PLUGSi/PLUGSi/PCB/1. Plug Base/Plug Base Circuit.png

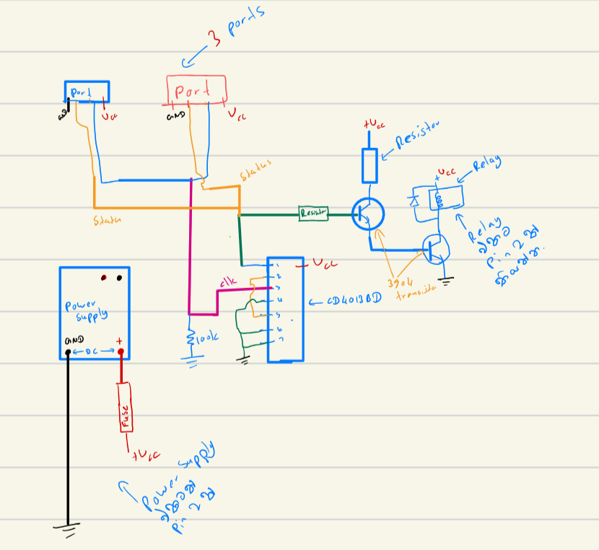
PCB/1. Plug Base/Plug Base Circuit.png
