PLUGSi/PLUGSi/PCB/2. Reprogrammable Timer/Timer Circuit.png

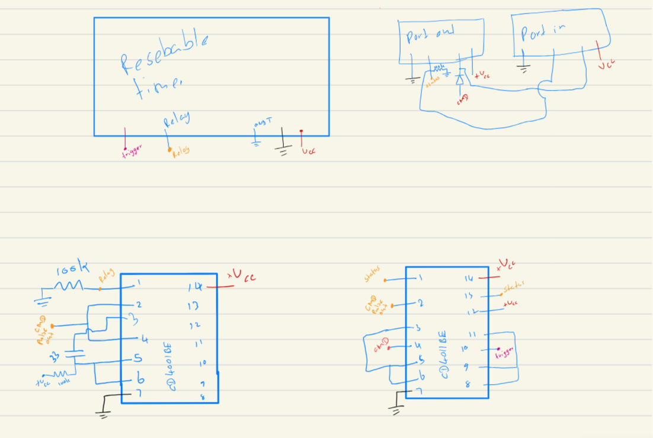
PCB/2. Reprogrammable Timer/Timer Circuit.png
