PLUGSi/PLUGSi/PCB/3. Set Timer/Set Timer Circuit.png

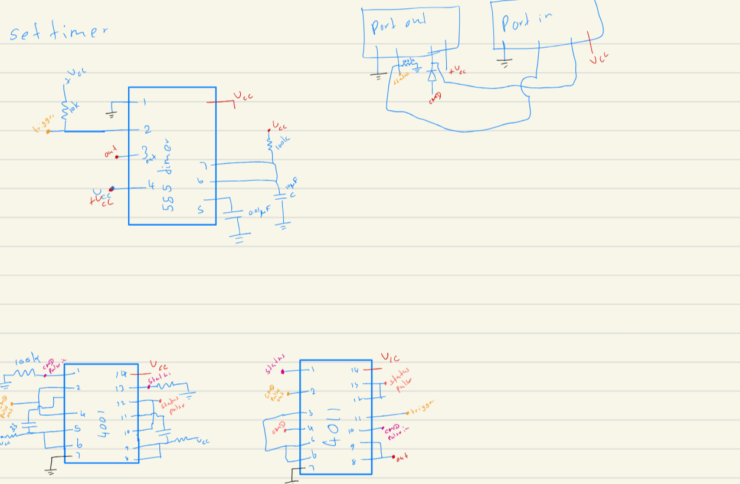
PCB/3. Set Timer/Set Timer Circuit.png
