PLUGSi/PLUGSi/Enclosure/Base/Base_Back.SLDPRT

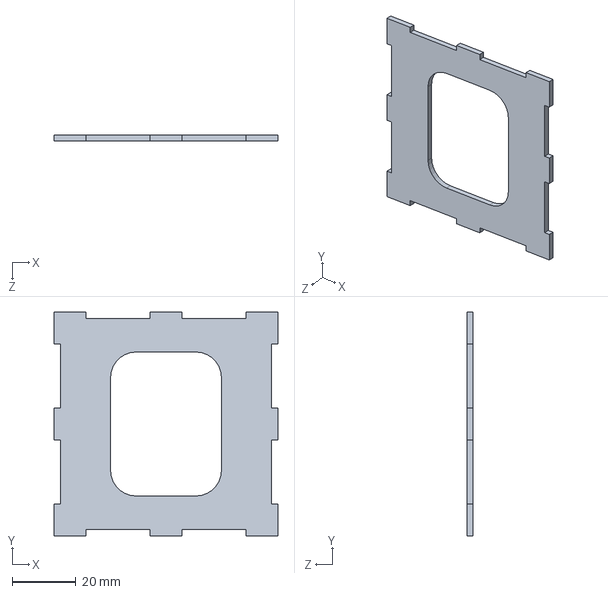
[picture p69: CAD file, 2024-06-27]
Enclosure/Base/Base_Back.SLDPRT
70.0 x 70.0 x 2.00 mm
