PLUGSi/PLUGSi/Enclosure/Module_Normal/DXF/Black/Module_LR_Female-1.DXF

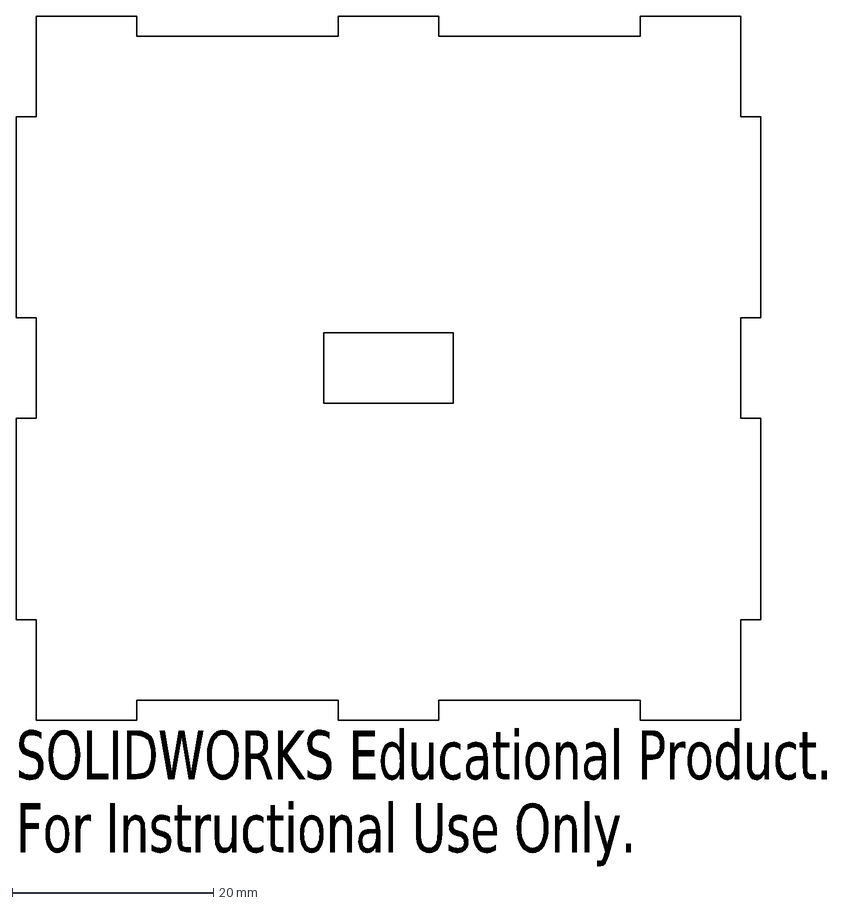
[picture p70: CAD file, 2024-06-27]
Enclosure/Module_Normal/DXF/Black/Module_LR_Female-1.DXF
SOLIDWORKS Educational Product.
For Instructional Use Only.
