PLUGSi/PLUGSi/Enclosure/Base/220ACto5VDC.SLDPRT

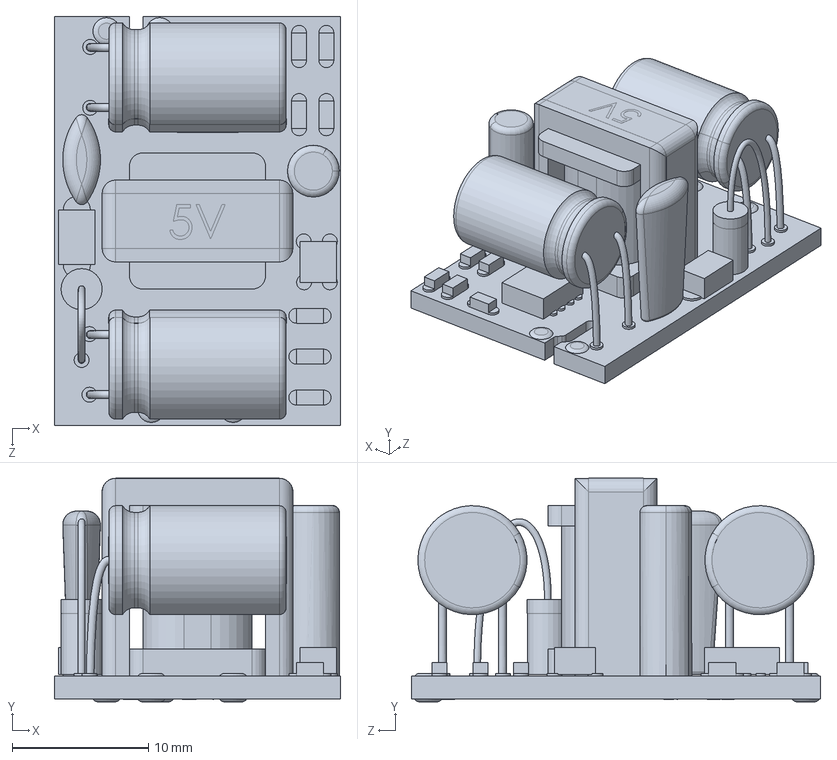
[picture p71: CAD file, 2024-06-27]
Enclosure/Base/220ACto5VDC.SLDPRT
21.0 x 16.4 x 30.0 mm
