PLUGSi/PLUGSi/Enclosure/Module/Module_Back.SLDPRT

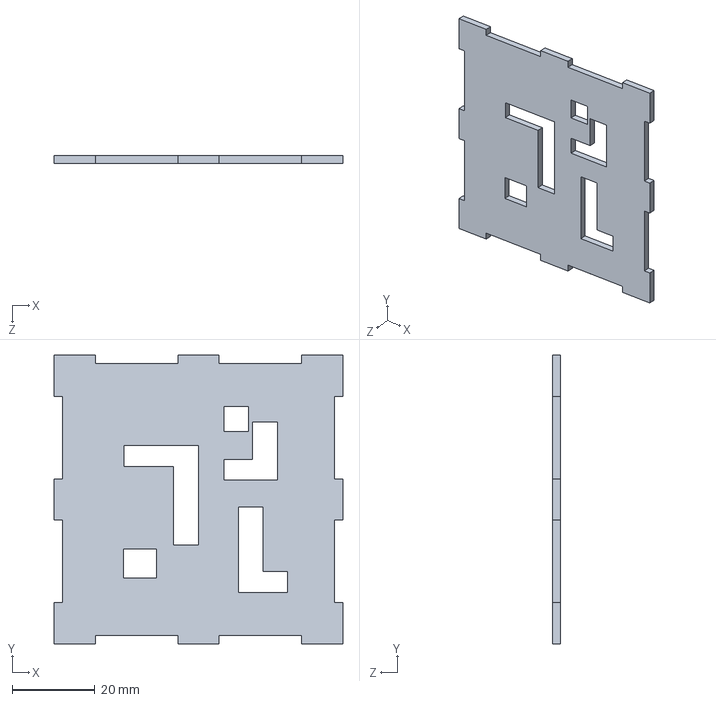
[picture p72: CAD file, 2024-06-27]
Enclosure/Module/Module_Back.SLDPRT
70.0 x 70.0 x 2.00 mm
