PLUGSi/PLUGSi/Enclosure/Module_Normal/Black_Cover.SLDPRT

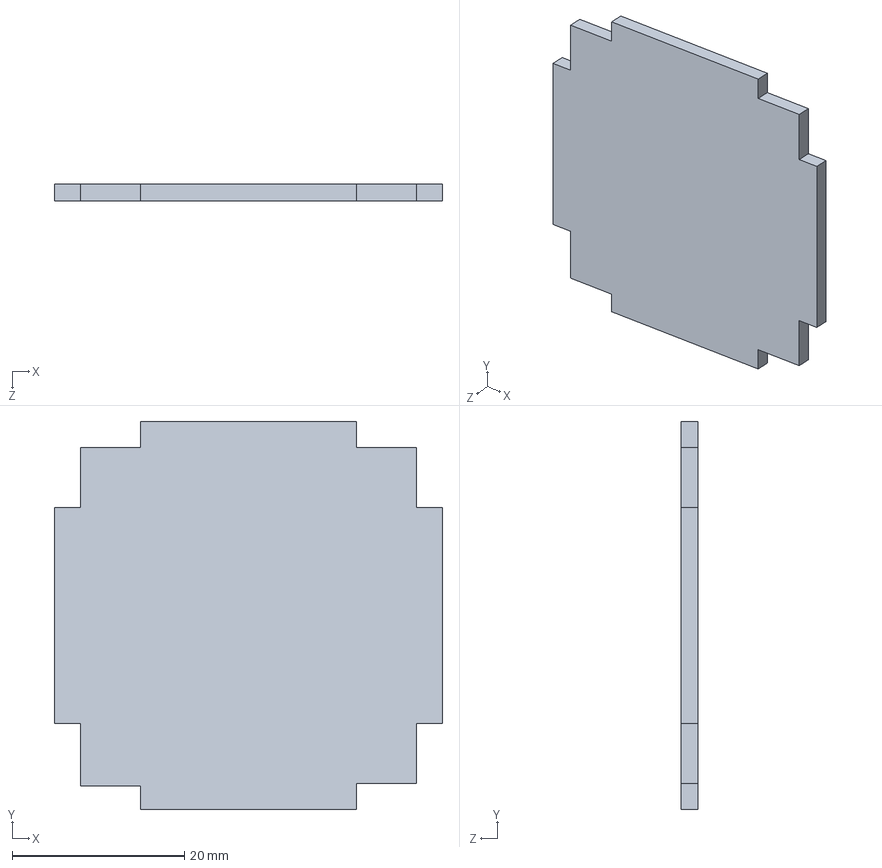
[picture p73: CAD file, 2024-06-27]
Enclosure/Module_Normal/Black_Cover.SLDPRT
45.0 x 45.0 x 2.00 mm
