PLUGSi/PLUGSi/Enclosure/Module/port_1.SLDPRT

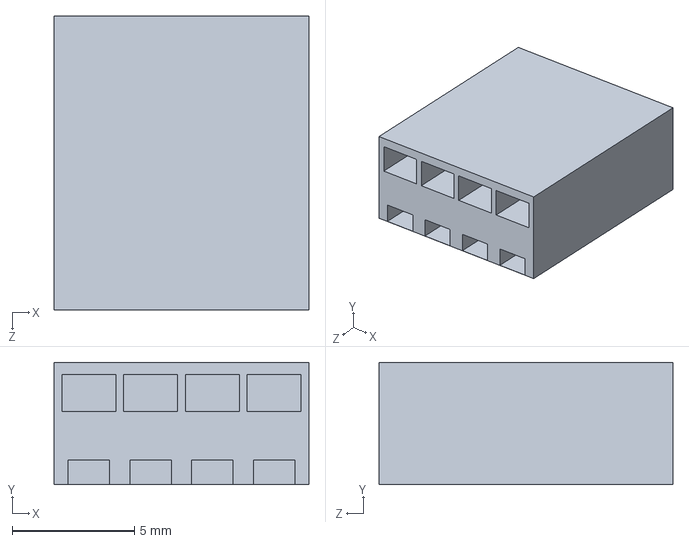
[picture p74: CAD file, 2024-06-27]
Enclosure/Module/port_1.SLDPRT
10.4 x 5.00 x 12.0 mm
