PLUGSi/PLUGSi/Enclosure/Base/Base_Plug_Front.SLDPRT

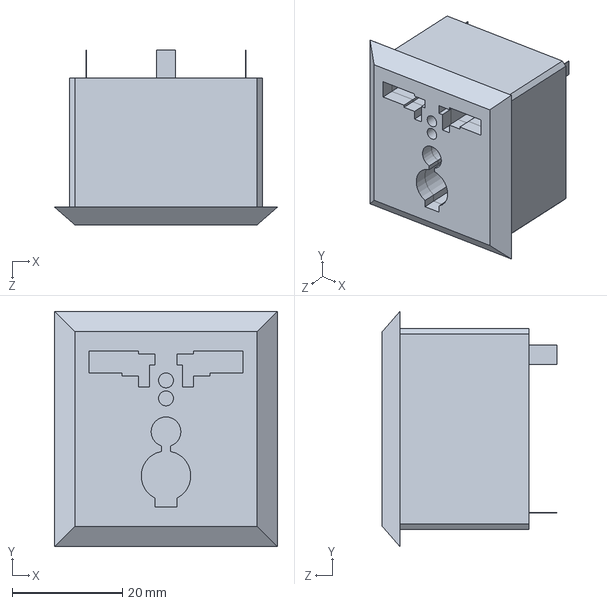
[picture p75: CAD file, 2024-06-27]
Enclosure/Base/Base_Plug_Front.SLDPRT
40.5 x 42.7 x 31.7 mm
