PLUGSi/PLUGSi/Enclosure/Module/Module_Front.SLDPRT

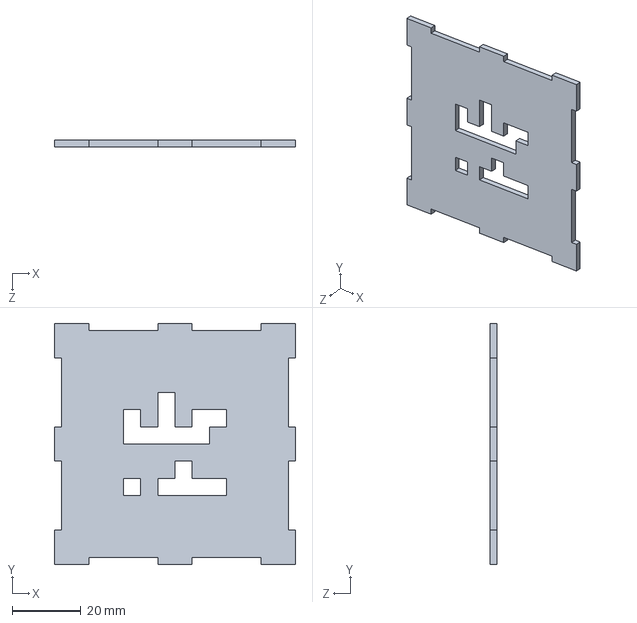
[picture p76: CAD file, 2024-06-27]
Enclosure/Module/Module_Front.SLDPRT
70.0 x 70.0 x 2.00 mm
