PLUGSi/PLUGSi/Enclosure/Module_Normal/fixer.SLDPRT

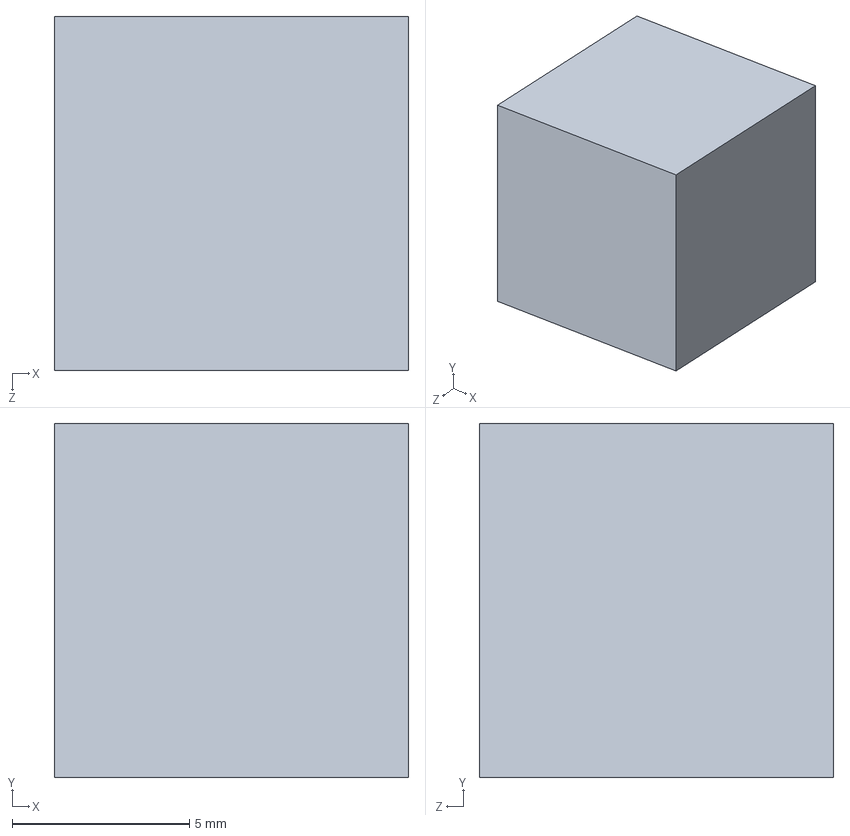
[picture p77: CAD file, 2024-06-27]
Enclosure/Module_Normal/fixer.SLDPRT
10.0 x 10.0 x 10.0 mm
